AndresRJ18/QUIM-DETECT2/PROYECTOS-DE-INGENIERIA-I/Entregables/Actividades/Certificados TLR/matihuerta.c@gmail.com-Gestion-de-la-madurez-tecnologica-TRL-Technology-readiness-levels-Constancia-Niveles-de-Madurez-Tecnologica-2023-Vinculate-Cursos.pdf

# CONSTANCIA DE PARTICIPACIÓN

Se otorga a:

MATIAS DARIO HUERTA CRUZ

Por finalizar satisfactoriamente el curso MOOC:

Gestión de la madurez tecnológica : TRL (Technology readiness levels)

Esfuerzo: 20 horas
Octubre 28, 2025, 4:01 pm
Brindado por CONCYTEC a través de la Plataforma Vincúlate
