AndresRJ18/QUIM-DETECT2/PROYECTOS-DE-INGENIERIA-I/Entregables/Partes3d/Tapa_Sup/Inf/MEDIDAS TAPA SUPERIOR E INFERIOR.pdf

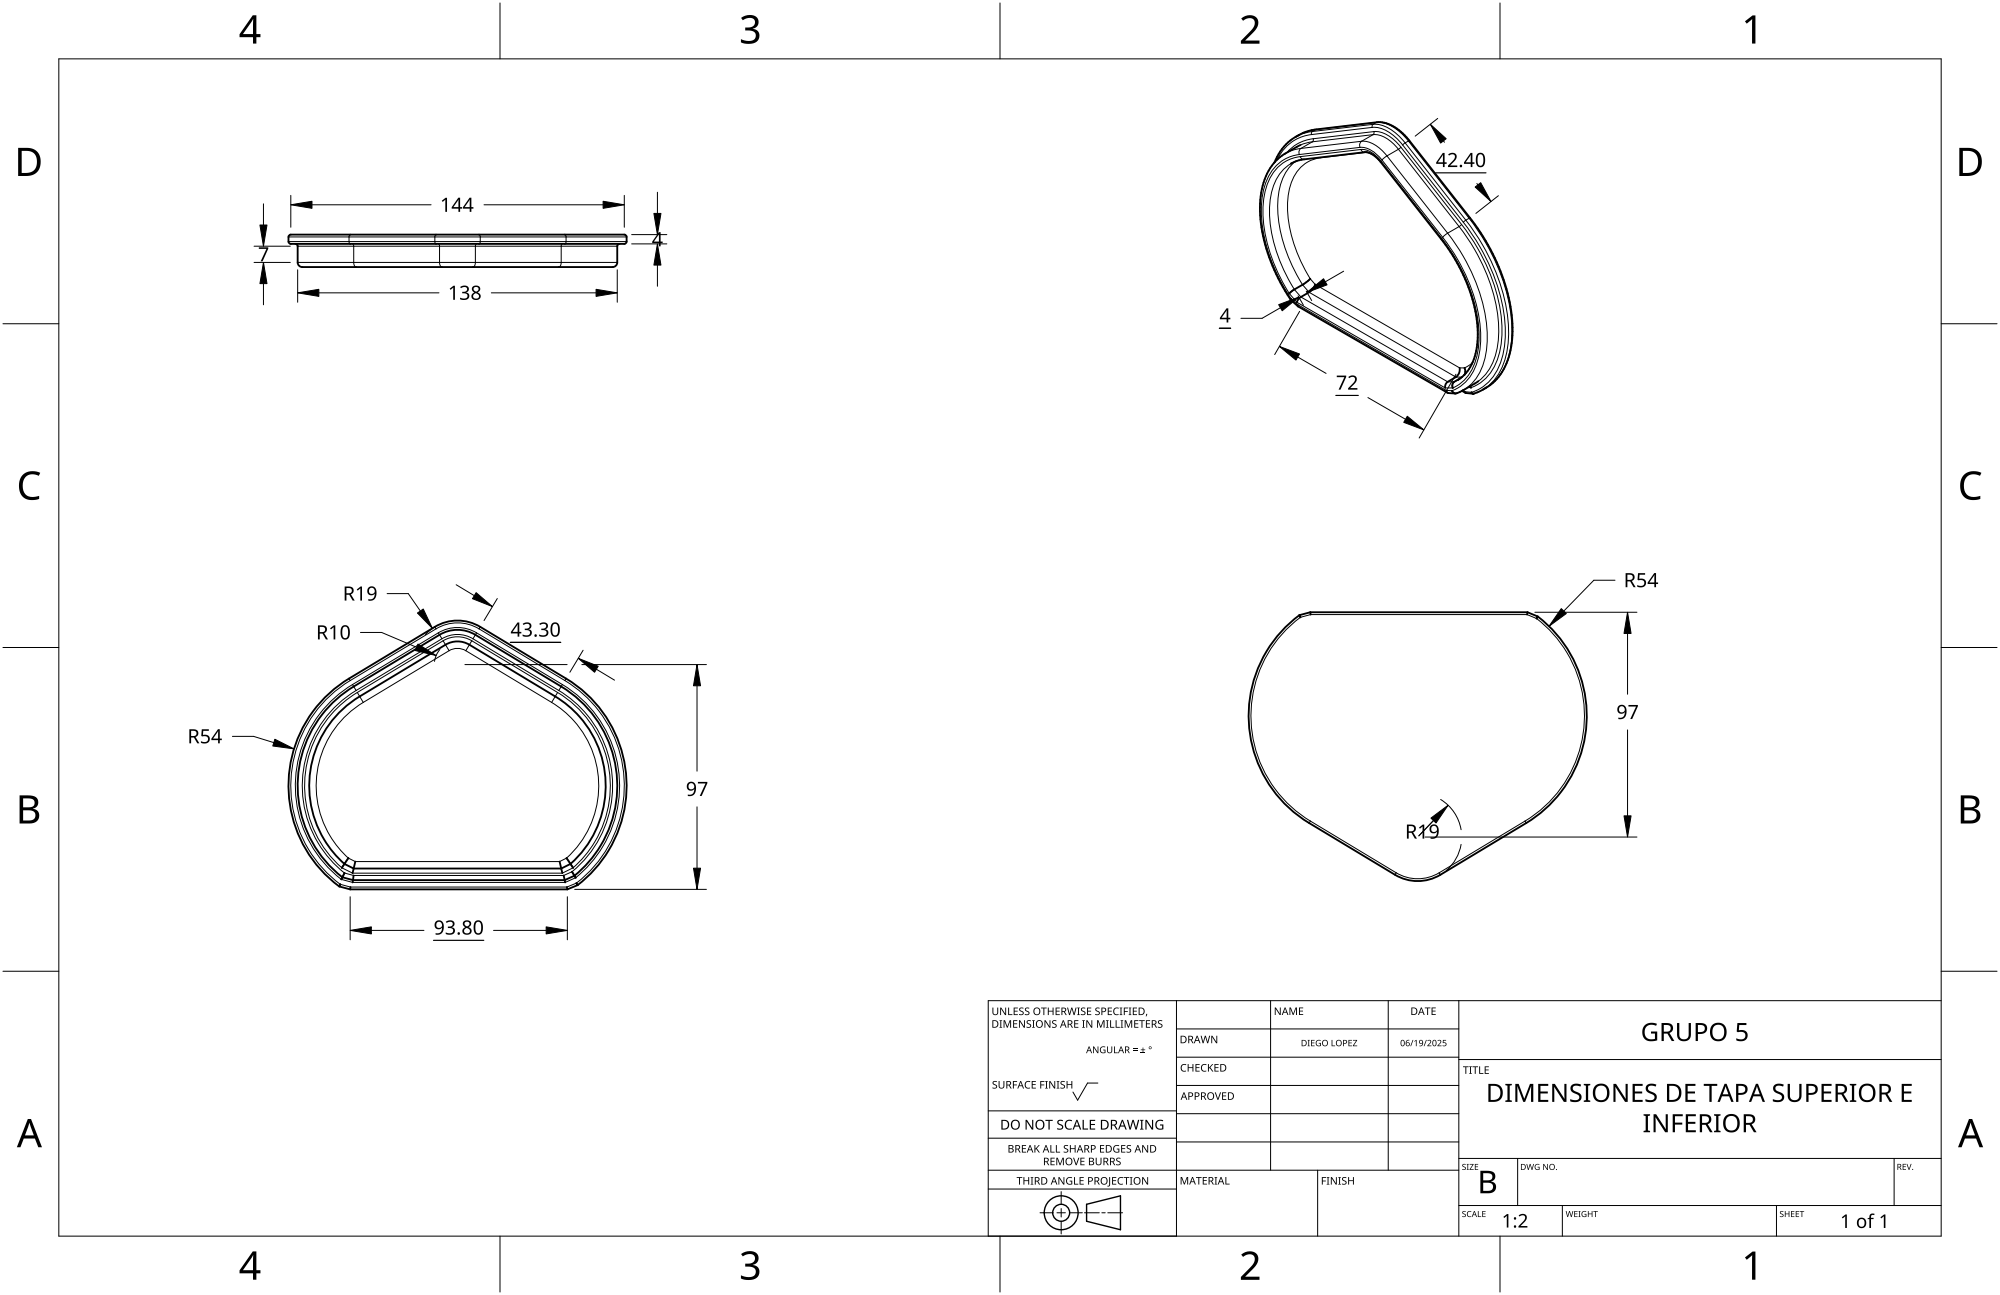
[picture p34: page 1]
